tomikaa87/led-timer/Images/case-v1-left-front.png

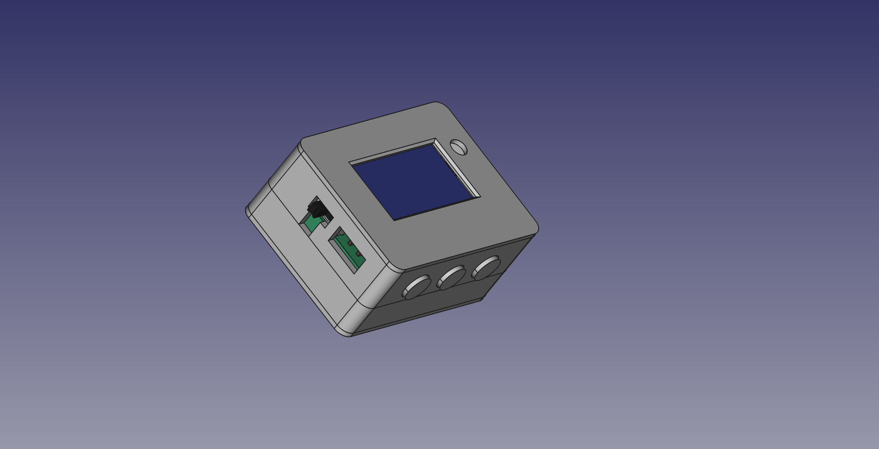
Images/case-v1-left-front.png
