tomikaa87/led-timer/Images/IMG_2652.jpg

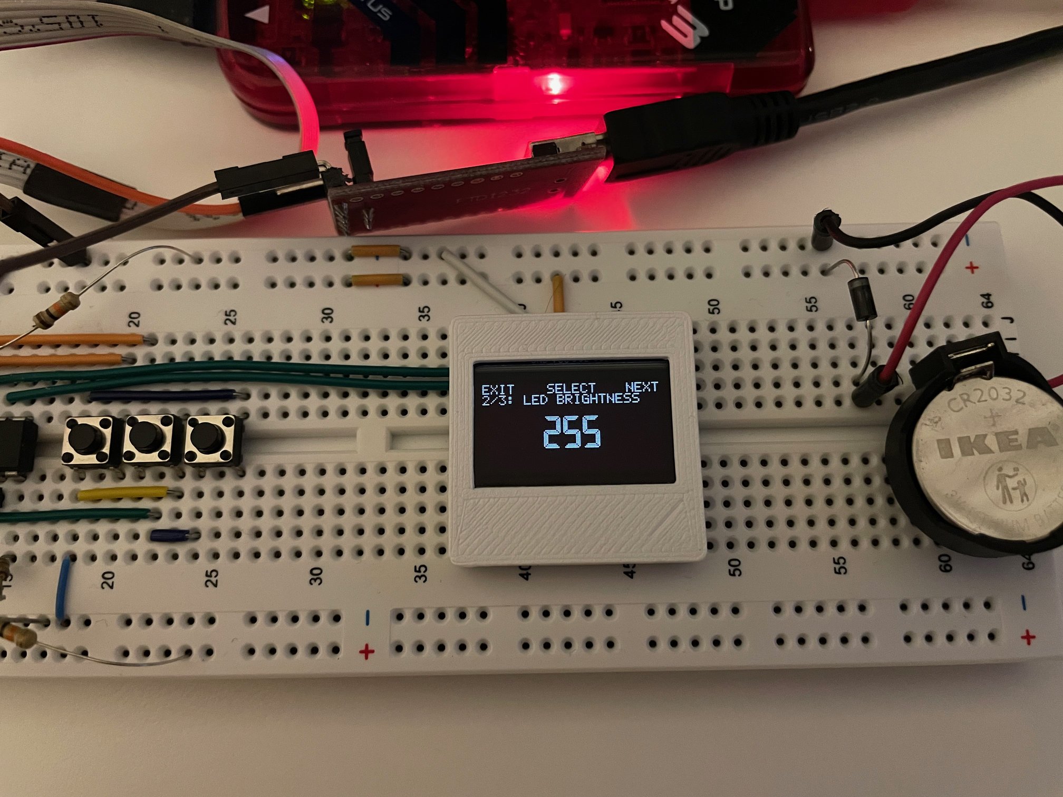
Images/IMG_2652.jpg
