tomikaa87/led-timer/Software/LEDTimer.X/MainScreen.c

/*
    This file is part of LEDTimer.

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
    Author: Tamas Karpati
    Created on 2022-12-03
*/

#include "Clock.h"
#include "Graphics.h"
#include "MainScreen.h"
#include "Settings.h"
#include "SSD1306.h"
#include "System.h"
#include "Text.h"
#include "Keypad.h"
#include "OutputController.h"

#include <stdio.h>

#pragma warning push
#pragma warning disable 763

static struct MainScreenContext {
    uint8_t scheduleSegmentIndex;
} context = {
    .scheduleSegmentIndex = 0
};

static void drawOutputToggleKeyHelp()
{
    static const uint8_t SwitchOffStateIcon[] = {
        0b00111100,
        0b01111110,
        0b11111111,
        0b11111111,
        0b11111111,
        0b11111111,
        0b11111111,
        0b11111111,
        0b10111101,
        0b10000001,
        0b10000001,
        0b10000001,
        0b10111101,
        0b10100101,
        0b10111101,
        0b10000001,
        0b10000001,
        0b10000001,
        0b01000010,
        0b00111100
    };

    static const uint8_t SwitchOnStateIcon[] = {
        0b00111100,
        0b01000010,
        0b10000001,
        0b10000001,
        0b10000001,
        0b10000001,
        0b10111101,
        0b10000001,
        0b10000001,
        0b10000001,
        0b10000001,
        0b10111101,
        0b11111111,
        0b11111111,
        0b11111111,
        0b11111111,
        0b11111111,
        0b11111111,
        0b01111110,
        0b00111100
    };

    static const uint8_t width =
        sizeof(Graphics_MiniBulbIcon)
        + sizeof(SwitchOffStateIcon);

    Graphics_drawBitmap(Graphics_MiniBulbIcon, 5, 64 - width / 2, 7, 0);

    Graphics_drawBitmap(
        OutputController_outputEnableTargetState()
            ? SwitchOffStateIcon
            : SwitchOnStateIcon,
        sizeof(SwitchOnStateIcon),
        64 - width / 2 + 7,
        7,
        0
    );
}

static void drawKeypadHelpBar()
{
    SSD1306_fillArea(0, 7, 128, 1, SSD1306_COLOR_BLACK);

    Graphics_drawKeypadHelpBarSeparators();

#if 0
    static const uint8_t SettingsIcon[] = {
        0b01001001,
        0b01001001,
        0b01001001,
        0b01001001,
        0b01001001,
        0b01001001,
    };

    Graphics_drawBitmap(SettingsIcon, 6, 1, 7, 0);
#else
    SSD1306_fillAreaPattern(1, 7, 6, 1, 0b01001001);
#endif

    drawOutputToggleKeyHelp();
}

static void drawClock()
{
    char s[6];
//    snprintf(s, sizeof(s), "%02u:%02u", hours, minutes);
    sprintf(s, "%02u:%02u", Clock_getHour(), Clock_getMinute());

    Text_draw7Seg(s, 3, 15, false);
}

static void drawScheduleWidget(const bool redraw)
{
    if (redraw) {
        // Fill the background
        SSD1306_fillArea(0, 0, 128, 2, SSD1306_COLOR_BLACK);
    }

    switch (Settings_data.scheduler.type) {
        case Settings_SchedulerType_Interval: {
            int8_t index = -1;
            bool on = false;

            Graphics_drawBitmap(
                Graphics_ArrowRightIcon,
                Graphics_ArrowRightIconWidth,
                1,
                0,
                0
            );

            const uint8_t StartPos = Graphics_ArrowRightIconWidth + 6;

            if (
                OutputController_getNextTransition(
                    Clock_getMinutesSinceMidnight(),
                    &index,
                    &on
                )
            ) {
                struct IntervalSwitch* sw = NULL;

                if (on) {
                    sw = &Settings_data.scheduler.intervals[index].onSwitch;
                } else {
                    sw = &Settings_data.scheduler.intervals[index].offSwitch;
                }

                Clock_Time transitionTime = OutputController_calculateSwitchTime(sw);

                uint8_t hours = (uint8_t)(transitionTime / 60);
                uint8_t minutes = (uint8_t)(transitionTime - hours * 60);

                uint8_t x = Text_draw(on ? "ON:  " : "OFF: ", 0, StartPos, 0, false);

                char buf[25] = { 0 };
                sprintf(buf, "%2u:%02u", hours, minutes);
                x = Text_draw(buf, 0, x, 0, false);

                // Sun-based switch time indicator
                if (
                    sw->type == Settings_IntervalSwitchType_Sunrise
                    || sw->type == Settings_IntervaSwitchType_Sunset
                ) {
                    x = 128
                        - Graphics_SunOnTheHorizonIconWidth
                        - 1
                        - Graphics_ArrowDownIconWidth
                        - 5
                        - CalculateTextWidth("+00")
                        - 1;

                    Graphics_DrawIcon(x, 0, Graphics_SunOnTheHorizonIcon);

                    x += Graphics_SunOnTheHorizonIconWidth + 1;
                    Graphics_drawBitmap(
                        Graphics_ArrowDownIcon,
                        Graphics_ArrowDownIconWidth,
                        x,
                        0,
                        sw->type == Settings_IntervalSwitchType_Sunrise
                            ? GRAPHICS_DRAW_FLIPX
                            : 0
                    );

                    FormatSunOffset(buf, sw->sunOffset);
                    x += Graphics_ArrowDownIconWidth + 5;
                    x = Text_draw(buf, 0, x, 0, false);
                }
            } else {
                Text_draw("---: --:--", 0, StartPos, 0, false);
            }

            break;
        }

        case Settings_SchedulerType_Segment: {
            if (redraw) {
                Graphics_drawScheduleBar(
                    0,
                    Settings_data.scheduler.segmentData,
                    GRAPHICS_DRAW_SCHEDULE_BAR_FLIP
                );
            }

            uint8_t segmentIndex = Types_calculateScheduleSegmentIndex(
                Clock_getMinutesSinceMidnight()
            );

            if (context.scheduleSegmentIndex != segmentIndex || redraw) {
                context.scheduleSegmentIndex = segmentIndex;
                Graphics_drawScheduleSegmentIndicator(2, segmentIndex, GRAPHICS_DRAW_SCHEDULE_BAR_FLIP);
            }

            break;
        }
    }
}

static void drawBulbIcon(const bool visible)
{
    static const uint8_t X = 127 - Graphics_BulbIconWidth - 15;

    if (visible) {
        Graphics_drawMultipageBitmap(
            (const uint8_t*)Graphics_BulbIcon,
            Graphics_BulbIconWidth,
            Graphics_BulbIconPages,
            X,
            3,
            false
        );
    } else {
        SSD1306_fillArea(
            X,
            3,
            Graphics_BulbIconWidth,
            Graphics_BulbIconPages,
            SSD1306_COLOR_BLACK
        );
    }
}

static void drawPowerIndicator()
{
    // TODO use the PowerInputChanged event in the future
    static bool lastPowerInputType = false;

    static const uint8_t BatteryIndicatorWidth =
        Graphics_BatteryIndicatorCapWidth
        + Graphics_BatteryIndicatorBodyFullWidth * 10
        + Graphics_BatteryIndicatorEndCapWidth;

    if (System_isRunningFromBackupBattery() != lastPowerInputType) {
        lastPowerInputType = System_isRunningFromBackupBattery();

        static const uint8_t ClearWidth =
            (BatteryIndicatorWidth > Graphics_ExternalPowerIndicatorWidth)
                ? BatteryIndicatorWidth
                : Graphics_ExternalPowerIndicatorWidth;

        SSD1306_fillArea(127 - ClearWidth, 7, ClearWidth, 1, SSD1306_COLOR_BLACK);
    }

    if (System_isRunningFromBackupBattery()) {
        uint8_t x = 127 - BatteryIndicatorWidth;

        Graphics_drawBitmap(
            (uint8_t*)Graphics_BatteryIndicatorCap,
            Graphics_BatteryIndicatorCapWidth,
            x,
            7,
            0
        );

        x += Graphics_BatteryIndicatorCapWidth;

        for (uint8_t i = 10 - System_getBatteryLevel(); i > 0; --i) {
            Graphics_drawBitmap(
                (uint8_t*)Graphics_BatteryIndicatorBodyEmpty,
                Graphics_BatteryIndicatorBodyEmptyWidth,
                x,
                7,
                0
            );

            ++x;
        }

        for (uint8_t i = System_getBatteryLevel(); i > 0; --i) {
            Graphics_drawBitmap(
                (uint8_t*)Graphics_BatteryIndicatorBodyFull,
                Graphics_BatteryIndicatorBodyFullWidth,
                x,
                7,
                0
            );

            ++x;
        }

        Graphics_drawBitmap(
            (uint8_t*)Graphics_BatteryIndicatorEndCap,
            Graphics_BatteryIndicatorEndCapWidth,
            x,
            7,
            0
        );
    } else {
        static const uint8_t X = 127 - Graphics_ExternalPowerIndicatorWidth;

        Graphics_drawBitmap(
            (uint8_t*)Graphics_ExternalPowerIndicator,
            Graphics_ExternalPowerIndicatorWidth,
            X,
            7,
            0
        );
    }
}

void MainScreen_update(const bool redraw)
{
    if (redraw) {
        drawKeypadHelpBar();
    }

    drawBulbIcon(OutputController_isOutputEnabled());
    drawClock();
    drawScheduleWidget(redraw);
    drawOutputToggleKeyHelp();
    drawPowerIndicator();
}

bool MainScreen_handleKeyPress(const uint8_t keyCode, const bool hold)
{
    switch (keyCode) {
        // Propagate to the UI to show the Settings
        case Keypad_Key1:
            break;

        case Keypad_Key2:
            if (!hold) {
                OutputController_toggle();
                return true;
            }
            break;

        // Key3 does nothing
        case Keypad_Key3:
            return true;
    }

    return false;
}

#pragma warning pop
