tomikaa87/led-timer/Software/LEDTimer.X/Text.c

/*
    This file is part of LEDTimer.

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
    Author: Tamas Karpati
    Created on 2022-11-29
*/

#include "Text.h"
#include "SSD1306.h"
#include "Graphics.h"

#include <ctype.h>
#include <string.h>

#define ASCIIReduced_CharCount              58
#define ASCIIReduced_SpaceWidth             5
#define ASCIIReduced_CharSpacing            1
#define ASCIIReduced_CharWidth              5

#define Numbers7Seg_CharCount               10
#define Numbers7Seg_CharWidth               12
#define Numbers7Seg_CharSpacing             2
#define Numbers7Seg_Pages                   3

static const uint8_t ASCIIReduced[ASCIIReduced_CharCount][ASCIIReduced_CharWidth] = {
    // !
    {
        0b00000000,
        0b00000000,
        0b01001111,
        0b00000000,
        0b00000000
    },
    // "
    {
        0b00000000,
        0b00000111,
        0b00000000,
        0b00000111,
        0b00000000
    },
    // #
    {
        0b00010100,
        0b01111111,
        0b00010100,
        0b01111111,
        0b00010100
    },
    // $
    {
        0b00100100,
        0b00101010,
        0b01111111,
        0b00101010,
        0b00010010
    },
    // %
    {
        0b00100011,
        0b00010011,
        0b00001000,
        0b01100100,
        0b01100010
    },
    // &
    {
        0b00110110,
        0b01001001,
        0b01010101,
        0b00100010,
        0b01010000
    },
    // '
    {
        0b00000000,
        0b00000101,
        0b00000011,
        0b00000000,
        0b00000000
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
            0b11110111,
            0b11111111
        },
        // 8, Page 2
        {
            0b00111111,
            0b01011111,
            0b01101111,
            0b01110000,
            0b01110000,
            0b01110000,
            0b01110000,
            0b01110000,
            0b01110000,
            0b01101111,
            0b01011111,
            0b00111111
        }
    },
    {
        // 9, Page 0
        {
            0b11111110,
            0b11111101,
            0b11111011,
            0b00000111,
            0b00000111,
            0b00000111,
            0b00000111,
            0b00000111,
            0b00000111,
            0b11111011,
            0b11111101,
            0b11111110
        },
        // 9, Page 1
        {
            0b00001111,
            0b00010111,
            0b00011011,
            0b00011100,
            0b00011100,
            0b00011100,
            0b00011100,
            0b00011100,
            0b00011100,
            0b11101011,
            0b11110111,
            0b11111111
        },
        // 9, Page 2
        {
            0b00000000,
            0b01000000,
            0b01100000,
            0b01110000,
            0b01110000,
            0b01110000,
            0b01110000,
            0b01110000,
            0b01110000,
            0b01101111,
            0b01011111,
            0b00111111
        }
    }
};

#define Colon7Seg_CharWidth                 4
#define Colon7Seg_Pages                     3
static const uint8_t Colon7Seg[Colon7Seg_Pages][Colon7Seg_CharWidth] = {
    {
        0b10000000,
        0b11000000,
        0b11000000,
        0b11000000
    },
    {
        0b10000011,
        0b11000011,
        0b11000011,
        0b11000001
    },
    {
        0b00000011,
        0b00000011,
        0b00000011,
        0b00000001
    }
};

#define Plus7Seg_CharWidth                  7
static const uint8_t Plus7Seg[Plus7Seg_CharWidth] = {
    0b00011100,
    0b00011100,
    0b01111111,
    0b01111111,
    0b01111111,
    0b00011100,
    0b00011100
};

uint8_t Text_draw(
    const char* s,
    const uint8_t line,
    uint8_t x,
    const uint8_t yOffset,
    const bool invert
)
{
    uint8_t length = (uint8_t)strlen(s);

    if (length == 0 || line > 7 || x > 127) {
        return x;
    }

    SSD1306_enablePageAddressing();
    SSD1306_setPage(line);

    uint8_t sendFlags = SSD1306_SEND_BITSHIFT(yOffset);
    if (invert) {
        sendFlags |= SSD1306_SEND_INVERT;
    }

    for (uint8_t i = length; i > 0; --i) {
        // Stop if the next character won't fit
        if (x > SSD1306_LCDWIDTH - 1) {
            return x;
        }

        SSD1306_setStartColumn(x);

        char c = (char)toupper(*s++);

        if (c == ' ') {
            for (uint8_t j = ASCIIReduced_SpaceWidth; j > 0; --j) {
                const uint8_t data = 0;
                SSD1306_sendData2(&data, 1, sendFlags);
            }
        } else {
            const uint8_t* charData;

            // If character is not supported, draw placeholder
            // Since space is dynamically generated, the first character is '!'
            if ((c - '!') >= ASCIIReduced_CharCount) {
                charData = ASCIIReducedPlaceholder;
            } else {
                // Get data for the next character
                charData = ASCIIReduced[c - '!'];
            }

            // Send data to the display
            SSD1306_sendData2(charData, ASCIIReduced_CharWidth, sendFlags);
        }

        x += ASCIIReduced_CharWidth;

        // Clear the pixels between the characters
        for (uint8_t j = ASCIIReduced_CharSpacing; j > 0; --j) {
            static const uint8_t data = 0;
            SSD1306_sendData2(&data, 1, sendFlags);
            ++x;
        }
    }

    return x;
}

uint8_t Text_draw7Seg(
    const char* number,
    const uint8_t line,
    uint8_t x,
    const bool invert
) {
    uint8_t length = (uint8_t)strlen(number);

    if (length == 0 || line > (7 - Numbers7Seg_Pages) || x > 127) {
        return x;
    }

    uint8_t sendFlags = 0;
    if (invert) {
        sendFlags |= SSD1306_SEND_INVERT;
    }

    SSD1306_enablePageAddressing();

    for (uint8_t i = length; i > 0; --i) {
        // Stop if the next character won't fit
        if (x + Numbers7Seg_CharWidth + 1 > SSD1306_LCDWIDTH - 1) {
            return x;
        }

        char c = *number++;

        if (c != ' ') {
            if (c == '-') {
                SSD1306_setStartColumn(x);
                SSD1306_setPage(line + 1);

                // Cost-efficient dash symbol
                uint8_t charData = 0b00011100;
                for (uint8_t j = Numbers7Seg_CharWidth - 5; j > 0; --j) {
                    SSD1306_sendData2(&charData, 1, sendFlags);
                }

                x += Numbers7Seg_CharWidth - 5 + Numbers7Seg_CharSpacing;
            } else if (c == '+') {
                SSD1306_setStartColumn(x);
                SSD1306_setPage(line + 1);
                SSD1306_sendData2(Plus7Seg, sizeof(Plus7Seg), sendFlags);

                x += Plus7Seg_CharWidth + Numbers7Seg_CharSpacing;
            } else {
                uint8_t width = Numbers7Seg_CharWidth;

                // Draw the pages of the character
                for (uint8_t page = 0; page < Numbers7Seg_Pages; ++page) {
                    SSD1306_setPage(line + page);
                    SSD1306_setStartColumn(x);

                    const uint8_t* charData = 0;

                    if (c >= '0' && c <= '9') {
                        charData = Numbers7Seg[c - '0'][page];
                    } else if (c == ':') {
                        width = Colon7Seg_CharWidth;
                        charData = Colon7Seg[page];
                    }

                    SSD1306_sendData2(charData, width, sendFlags);
                }

                x += width;

                if (i > 1) {
                    x += Numbers7Seg_CharSpacing;
                }
            }
        } else {
            for (uint8_t page = 0; page < Numbers7Seg_Pages; ++page) {
                SSD1306_setPage(line + page);
                SSD1306_setStartColumn(x);

                uint8_t charData[Numbers7Seg_CharWidth] = { 0 };
                SSD1306_sendData2(charData, sizeof(charData), sendFlags);
            }

            x += Numbers7Seg_CharWidth;

            if (i > 1) {
                x += Numbers7Seg_CharSpacing;
            }
        }
    }

    return x;
}

uint8_t Text_calculateWidth(const char* s)
{
    uint8_t width = 0;

    while (*s) {
        char c = *s++;

        if (c == ' ') {
            width += ASCIIReduced_SpaceWidth;
        } else {
            width += ASCIIReduced_CharWidth;
        }

        if (*s != 0) {
            width += ASCIIReduced_CharSpacing;
        }
    }

    return width;
}

uint8_t Text_calculateWidth7Seg(const char* s)
{
    uint8_t width = 0;

    while (*s) {
        char c = *s++;

        if ((c >= '0' && c <= '9') || c == ' ') {
            width += Numbers7Seg_CharWidth;
        } else if (c == ':') {
            width += Colon7Seg_CharWidth;
        } else if (c == '-') {
            width += Numbers7Seg_CharWidth - 2;
        } else if (c == '+') {
            width += Plus7Seg_CharWidth;
        }

        if (*s != 0) {
            width += Numbers7Seg_CharSpacing;
        }
    }

    return width;
}
