tomikaa87/led-timer/Software/LEDTimerLite.X/UserInterface.c

/*
    This file is part of LEDTimer.

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
    Author: Tamas Karpati
    Created on 2024-12-16
*/

#include "UserInterface.h"

#include "Clock.h"
#include "Config.h"
#include "OutputController.h"
#include "System.h"

#include <xc.h>

static struct UserInteraceContext {
    uint8_t ledLeaveOnAfterBlinking : 1;
    uint8_t ledBlinkCount : 3;
    uint8_t ledFastBlink : 1;
    uint8_t : 3;
    Clock_Ticks ledTicks;
} UserInterface_context = {
    .ledLeaveOnAfterBlinking = 0,
    .ledBlinkCount = 0,
    .ledFastBlink = 0,
    .ledTicks = 0
};

// Indicator LED control logic

static void LED_turnOn(void)
{
    UserInterface_context.ledBlinkCount = 0;
    INDICATOR_LED_OUTPUT = 1;
}

static void LED_turnOff(void)
{
    UserInterface_context.ledBlinkCount = 0;
    INDICATOR_LED_OUTPUT = 0;
}

static void LED_blink(const uint8_t count, const bool fast)
{
    if (count == 0) {
        INDICATOR_LED_OUTPUT = 0;
        return;
    }

    UserInterface_context.ledBlinkCount = count;
    UserInterface_context.ledFastBlink = fast;
    UserInterface_context.ledTicks = Clock_getFastTicks();
    INDICATOR_LED_OUTPUT = 1;
}

static void LED_task()
{
    if (UserInterface_context.ledBlinkCount > 0) {
        uint8_t interval = UserInterface_context.ledFastBlink ? 10 : 30;
        if (Clock_getFastTicks() - UserInterface_context.ledTicks >= interval) {
            if (!INDICATOR_LED_OUTPUT) {
                // Decrement only after a full on-off cycle
                --UserInterface_context.ledBlinkCount;
            }
            if (UserInterface_context.ledBlinkCount > 0 || UserInterface_context.ledLeaveOnAfterBlinking) {
                INDICATOR_LED_OUTPUT ^= 1;
            }
            UserInterface_context.ledTicks = Clock_getFastTicks();
        }
    }
}

// User interface logic

void UserInterface_init(void)
{
    LED_blink(1, false);
}

void UserInterface_runTasks(void)
{

}

void UserInterface_runLightweightTasks(void)
{
    LED_task();
}

bool UserInterface_hasPendingLightweightTasks(void)
{
    return UserInterface_context.ledBlinkCount > 0;
}

void UserInterface_buttonPressEvent(void)
{
    if (System_isRunningFromBackupBattery()) {
        LED_blink(3, true);
    } else {
        OutputController_toggle();
    }
}

inline void UserInterface_handleExternalEvent(const UI_ExternalEvent event)
{
    switch (event) {
        case UI_ExternalEvent_PowerInputChanged:
            if (System_isRunningFromBackupBattery()) {
                LED_blink(3, true);
            } else {
                if (!OutputController_isOutputEnabled()) {
                    LED_blink(1, false);
                }
            }
            break;

        case UI_ExternalEvent_OutputStateChanged:
            if (OutputController_isOutputEnabled()) {
                LED_turnOn();
            } else {
                LED_turnOff();
            }
            break;

        default:
            break;
    }
}
