tomikaa87/led-timer/Software/LEDTimer.X/SettingsScreen_Date.c

/*
    This file is part of LEDTimer.

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
    Author: Tamas Karpati
    Created on 2023-01-31
*/

#include "Clock.h"
#include "Graphics.h"
#include "Keypad.h"
#include "SettingsScreen_Date.h"
#include "Utils.h"

#include <stdbool.h>
#include <stdint.h>
#include <stdio.h>
#include <string.h>

static struct SettingScreen_Date_Context {
    YearsFrom1970 year;
    uint8_t month;
    uint8_t day;
    uint8_t lastDayOfMonth;
    uint8_t selectionIndex;
} context;

void SettingsScreen_Date_init()
{
    context.year = Clock_getYear();
    context.month = Clock_getMonth();
    context.day = Clock_getDay();
    context.lastDayOfMonth = Date_lastDayOfMonth(
        context.month,
        Date_isLeapYear(context.year)
    );
    context.selectionIndex = 0;
}

void SettingsScreen_Date_update(const bool redraw)
{
    if (redraw) {
        Graphics_DrawScreenTitle("DATE");
        Graphics_DrawKeypadHelpBar(Graphics_ExitIcon, Graphics_ArrowRightIcon, Graphics_AdjustIcon);
    }

    #define CharWidth 12u
    #define CharSpacing 2u
    #define TotalWidth (8u * CharWidth + 15u * CharSpacing)
    #define ExtraSpacing (CharSpacing * 4)
    #define LinePattern 0b00000110

    char s[5];
    uint8_t x = 64 - TotalWidth / 2;
    uint8_t xPrev = x;

    // Year
    sprintf(s, "%04u", (uint16_t)context.year + 1970);
    x = Text_draw7Seg(s, 2, x, false);
    SSD1306_fillAreaPattern(xPrev, 5, x - xPrev, 1, context.selectionIndex == 0 ? LinePattern : 0);
    x += ExtraSpacing;

    // Month
    sprintf(s, "%02u", context.month);
    xPrev = x;
    x = Text_draw7Seg(s, 2, x, false);
    SSD1306_fillAreaPattern(xPrev, 5, x - xPrev, 1, context.selectionIndex == 1 ? LinePattern : 0);
    x += ExtraSpacing - 1 /* to fit the last 2 numbers on the screen */;

    // Day
    sprintf(s, "%02u", context.day);
    xPrev = x;
    x = Text_draw7Seg(s, 2, x, false);
    SSD1306_fillAreaPattern(xPrev, 5, x - xPrev, 1, context.selectionIndex == 2 ? LinePattern : 0);
}

bool SettingsScreen_Date_handleKeyPress(const uint8_t keyCode, const bool hold)
{
    switch (keyCode) {
        // Exit
        case Keypad_Key1: {
            if (hold) {
                break;
            }

            Clock_setDate(context.year, context.month, context.day);

            return false;
        }

        // Change selection
        case Keypad_Key2: {
            if (++context.selectionIndex > 2) {
                context.selectionIndex = 0;
            }
            SettingsScreen_Date_update(false);
            break;
        }

        // Adjust the selected value
        case Keypad_Key3: {
            switch (context.selectionIndex) {
                case 0:
                    // Max year = 2050
                    if (++context.year > 80) {
                        context.year = 0;
                    }
                    context.lastDayOfMonth = Date_lastDayOfMonth(
                        context.month,
                        Date_isLeapYear(context.year)
                    );
                    if (context.day > context.lastDayOfMonth) {
                        context.day = context.lastDayOfMonth;
                    }
                    break;

                case 1:
                    if (++context.month > 12) {
                        context.month = 1;
                    }
                    context.lastDayOfMonth = Date_lastDayOfMonth(
                        context.month,
                        Date_isLeapYear(context.year)
                    );
                    if (context.day > context.lastDayOfMonth) {
                        context.day = context.lastDayOfMonth;
                    }
                    break;

                case 2:
                    if (++context.day > context.lastDayOfMonth) {
                        context.day = 1;
                    }
                    break;

                default:
                    break;
            }
            SettingsScreen_Date_update(false);
            break;
        }
    }

    return true;
}
