tomikaa87/led-timer/Software/LEDTimer.X/SettingsScreen_TimeZone.c

/*
    This file is part of LEDTimer.

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
    Author: Tamas Karpati
    Created on 2023-01-31
*/

#include "Clock.h"
#include "Graphics.h"
#include "Keypad.h"
#include "SettingsScreen_TimeZone.h"

#include <stdbool.h>
#include <stdint.h>
#include <stdio.h>
#include <stdlib.h>
#include <string.h>

static struct SettingScreen_TimeZone_Context {
    struct Time* settings;
} context;

void SettingsScreen_TimeZone_init(struct Time* settings)
{
    context.settings = settings;
}

void SettingsScreen_TimeZone_update(const bool redraw)
{
    if (redraw) {
        Graphics_DrawScreenTitle("TIME ZONE");
        Graphics_DrawKeypadHelpBarLeftRight(Graphics_ExitIcon, Graphics_AdjustIcon);
    }

    #define CharWidth 12u
    #define CharSpacing 2u
    #define ColonWidth 4u
    #define SignWidth 7u
    #define TotalWidth (4u * CharWidth + 1u * ColonWidth + 1u * SignWidth + 5u * CharSpacing)
    #define LinePattern 0b00000110

    char s[7];
    uint8_t x = 64u - TotalWidth / 2u;
    uint8_t xPrev = x;

    // Time zone
    sprintf(
        s,
        "%c%02u:%02u",
        context.settings->timeZoneOffsetHalfHours >= 0 ? '+' : '-',
        abs(context.settings->timeZoneOffsetHalfHours / 2),
        abs(context.settings->timeZoneOffsetHalfHours % 2) * 30
    );
    xPrev = x;
    x = Text_draw7Seg(s, 2, x, false);
    SSD1306_fillAreaPattern(xPrev, 5, x - xPrev, 1, LinePattern);
}

bool SettingsScreen_TimeZone_handleKeyPress(const uint8_t keyCode, const bool hold)
{
    switch (keyCode) {
        // Exit
        case Keypad_Key1: {
            if (hold) {
                break;
            }

            // Apply changes immediately to avoid the following scenario:
            // 1. Set the Time Zone to be different from UTC
            // 2. Set the local time in Time settings
            // 3. Exit the menu
            // ER: time is the correct local time
            // AR: time is off by the time zone offset, because without exiting the menu before
            //     setting the time, the previous time zone is used when setting the clock
            Settings_data.time.timeZoneOffsetHalfHours = context.settings->timeZoneOffsetHalfHours;

            return false;
        }

        // Change selection
        case Keypad_Key2: {
            break;
        }

        // Minutes
        case Keypad_Key3: {
            // -12:00 .. +14:00 in 30 minute steps
            if (++context.settings->timeZoneOffsetHalfHours > 28) {
                context.settings->timeZoneOffsetHalfHours = -24;
            }

            SettingsScreen_TimeZone_update(false);
            break;
        }
    }

    return true;
}
